nelsonii/pseudolog/DSCN8648.JPG

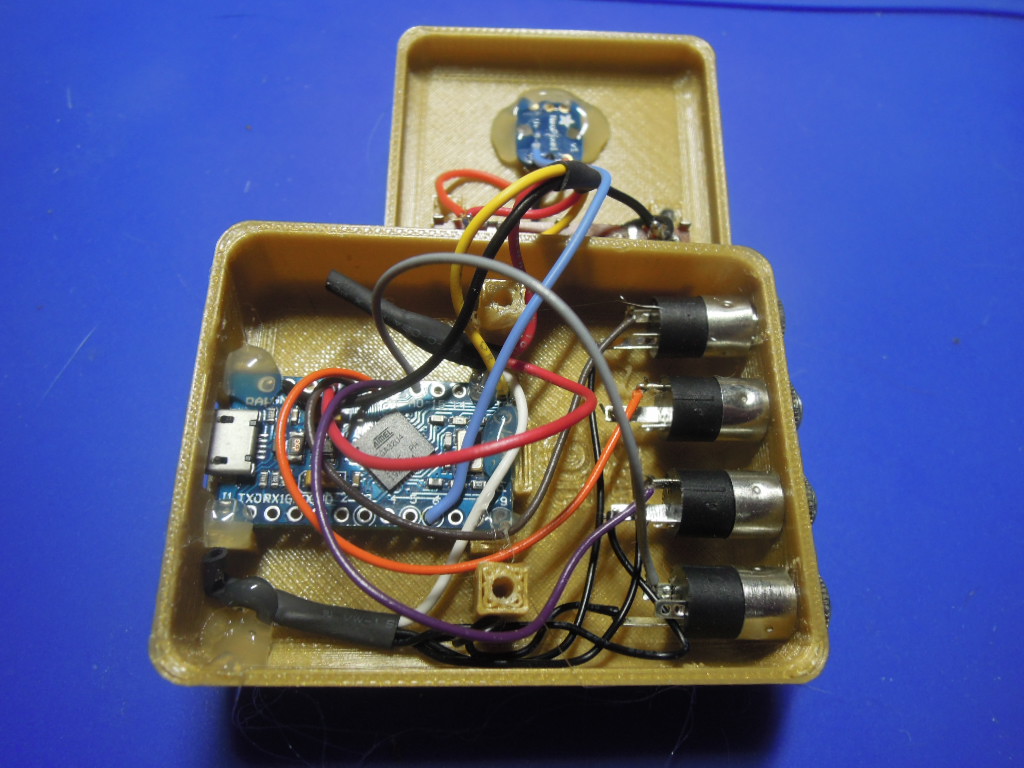
DSCN8648.JPG
