nelsonii/pseudolog/DSCN8649.JPG

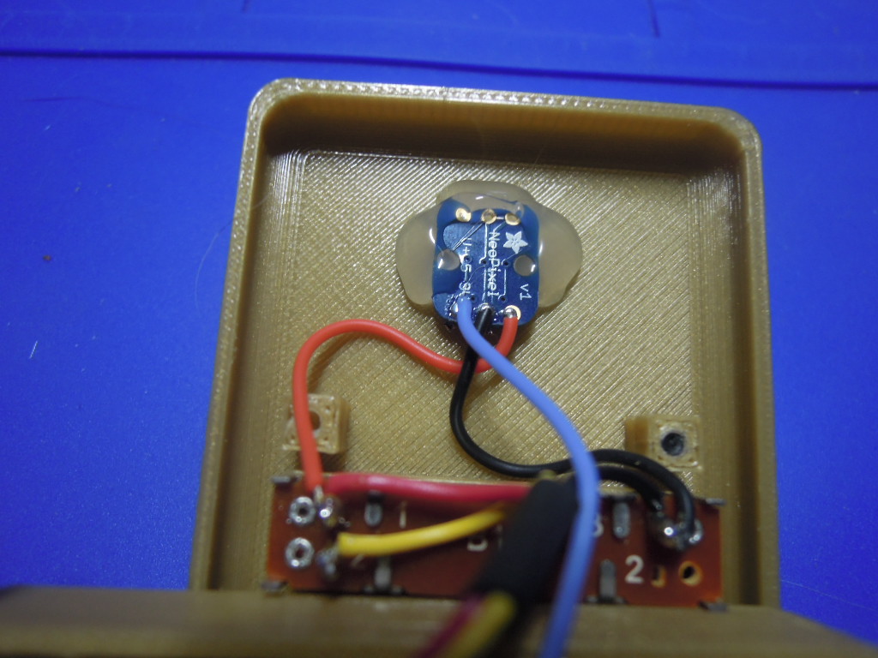
DSCN8649.JPG
