nelsonii/pseudolog/DSCN8650.JPG

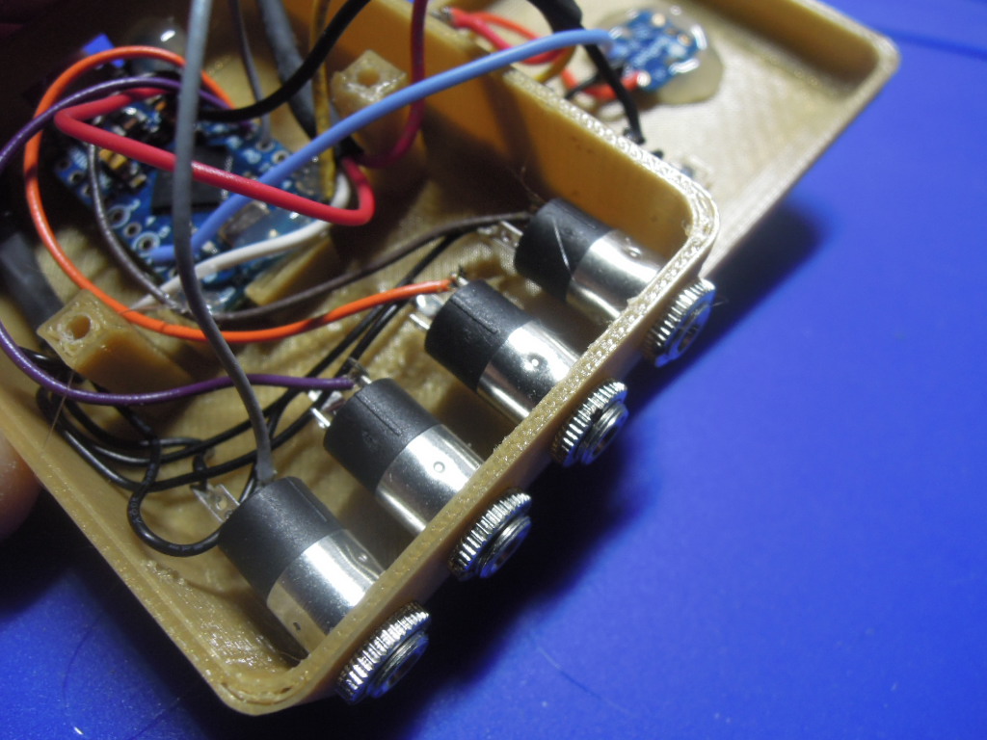
DSCN8650.JPG
