nelsonii/pseudolog/DSCN8652.JPG

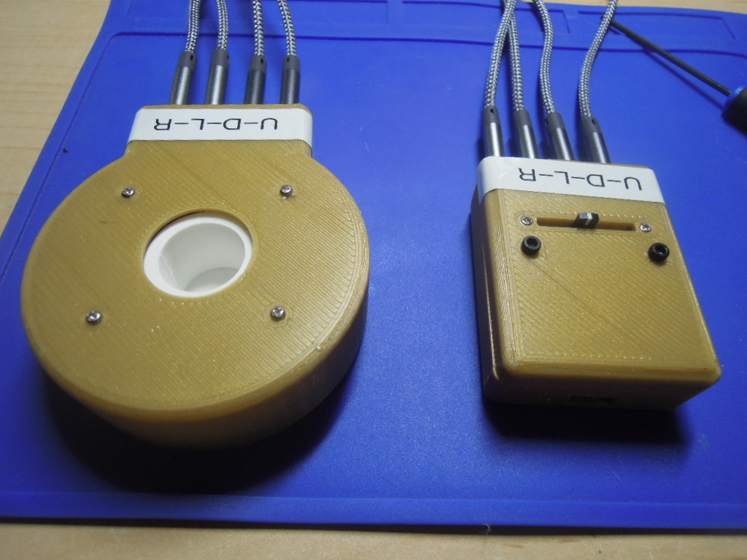
DSCN8652.JPG
